icl-rocketry/Ricardo-Kermit/Firmware/v3/src/Commands/commands.h

/**
 * @file commands.h
 * @author Kiran de Silva (kd619@ic.ac.uk)
 * @brief Contains signatures of all commands in the system. Note there is no requirement ot have all the command signatures defined in a single file, just ensure all the seperate files are included into the command_config.h
 * @version 0.1
 * @date 2023-06-17
 * 
 * @copyright Copyright (c) 2023
 * 
 */
#pragma once
#include <stdint.h>

#include "Config/forward_decl.h"
#include <librnp/rnp_packet.h>

namespace Commands{
    
    void FreeRamCommand(ForwardDecl_SystemClass& system, const RnpPacketSerialized& packet);
    void TelemetryCommand(System& sm, const RnpPacketSerialized& packet);
    void rawADCCommand(System& sm, const RnpPacketSerialized& packet);

}
