icl-rocketry/Ricardo-Kermit/Sensors/Software/src/ADS1219.cpp

#include <Wire.h>
#include "ADS1219.h"


ADS1219::ADS1219(TwoWire& wire, uint8_t addr) :
    _wire(wire)
{
  _i2cPort = &_wire;
  address = addr;
  config = 0x00;
  singleShot = true;
}

void ADS1219::begin(adsGain_t gain, int rate, adsMode_t mode, adsRef_t vref) {
  setGain(gain);
  setDataRate(rate);
  setConversionMode(mode);
  setVoltageReference(vref);
}

void ADS1219::start(){
  _i2cPort->beginTransmission(address);
  _i2cPort->write(0x08);
  _i2cPort->endTransmission();
}

void ADS1219::powerDown(){
  _i2cPort->beginTransmission(address);
  _i2cPort->write(0x02);
  _i2cPort->endTransmission();
}

uint8_t ADS1219::readRegister(uint8_t reg){
  _i2cPort->beginTransmission(address);
  _i2cPort->write(reg);
  _i2cPort->endTransmission();
  _i2cPort->requestFrom((uint8_t)address,(uint8_t)1);
  return _i2cPort->read();
}

void ADS1219::writeRegister(uint8_t data){
  _i2cPort->beginTransmission(address);
  _i2cPort->write(CONFIG_REGISTER_ADDRESS);
  _i2cPort->write(data);
  _i2cPort->endTransmission();
}

long ADS1219::readConversionResult(){
  _i2cPort->beginTransmission(address);
  _i2cPort->write(0x10);
  _i2cPort->endTransmission();
  _i2cPort->requestFrom((uint8_t)address,(uint8_t)3);
  long data32 = _i2cPort->read();
  data32 <<= 8;
  data32 |= _i2cPort->read();
  data32 <<= 8;
  data32 |= _i2cPort->read();
  return (data32 << 8) >> 8;
}

void ADS1219::resetConfig(){
	writeRegister(0x00);
}

long ADS1219::readSingleEnded(int channel){
	config &= MUX_MASK;
	switch (channel){
    case (0):
      config |= MUX_SINGLE_0;
      break;
    case (1):
      config |= MUX_SINGLE_1;
      break;
    case (2):
      config |= MUX_SINGLE_2;
      break;
    case (3):
      config |= MUX_SINGLE_3;
      break;
	default:
	  break;
  }
  writeRegister(config);
	  start();
	  return readConversionResult();
}

long ADS1219::readDifferential_0_1(){
  config &= MUX_MASK;
  config |= MUX_DIFF_0_1;
  writeRegister(config);
  start();
  return readConversionResult();
}

long ADS1219::readDifferential_2_3(){
  config &= MUX_MASK;
  config |= MUX_DIFF_2_3;
  writeRegister(config);
  start();
  return readConversionResult();
}

long ADS1219::readDifferential_1_2(){
  config &= MUX_MASK;
  config |= MUX_DIFF_1_2;
  writeRegister(config);
  start();
  return readConversionResult();
}

long ADS1219::readShorted(){
  config &= MUX_MASK;
  config |= MUX_SHORTED;
  writeRegister(config);
  return readConversionResult();
}

void ADS1219::setGain(adsGain_t gain){
  config &= GAIN_MASK;
  config |= gain;
  writeRegister(config);
}

void ADS1219::setDataRate(int rate){
	config &= DATA_RATE_MASK;
	switch (rate){
    case (20):
      config |= DATA_RATE_20;
      break;
    case (90):
      config |= DATA_RATE_90;
      break;
    case (330):
      config |= DATA_RATE_330;
      break;
    case (1000):
      config |= DATA_RATE_1000;
      break;
	default:
	  break;
  }
  writeRegister(config);
}

void ADS1219::setConversionMode(adsMode_t mode){
  config &= MODE_MASK;
  config |= mode;
  writeRegister(config);
  if (mode == CONTINUOUS){
	  singleShot = false;
  } else {
	  singleShot = true;
  }
}

void ADS1219::setVoltageReference(adsRef_t vref){
  config &= VREF_MASK;
  config |= vref;
  writeRegister(config);
}
